hannes-hochreiner/sensor-net-gateway-bl651/box/src/bottom.3d.scad

use <bottom.2d.scad>;

linear_extrude(height = 2, center = true, convexity = 10, twist = 0) {
  bottom();
}
