hannes-hochreiner/sensor-net-gateway-bl651/box/src/box_mount.2d.scad

module box_mount() {
  difference() {
    polygon(points=[
          [-3,-3],
          [3,-3],
          [3,3],
          [-3,3],
        ],convexity=10);
    circle(d=3.2, $fn=50);
  }
}

box_mount();
