hannes-hochreiner/sensor-net-gateway-bl651/box/src/combined.scad

include <front.3d.scad>
include <top.3d.scad>
include <left.3d.scad>
