hannes-hochreiner/sensor-net-gateway-bl651/box/src/front.2d.scad

use <../lib/side.scad>

module front() {
  side_front_back(36,12,2);
}

front();
