hannes-hochreiner/sensor-net-gateway-bl651/box/src/left.2d.scad

use <../lib/side.scad>

module left() {
  side_left_right(50.2,12,2);
}

left();
