hannes-hochreiner/sensor-net-gateway-bl651/box/src/mounting.3d.scad

use <mounting.2d.scad>;

linear_extrude(height = 2, center = true, convexity = 10, twist = 0) {
  mounting();
}
