hannes-hochreiner/sensor-net-gateway-bl651/box/src/pcb_mount.2d.scad

module pcb_mount() {
  difference() {
    circle(d=5.9, $fn=50);
    circle(d=3.2, $fn=50);
  }
}

pcb_mount();
