hannes-hochreiner/sensor-net-gateway-bl651/box/src/pcb_mount.3d.scad

use <pcb_mount.2d.scad>;

linear_extrude(height = 2, center = true, convexity = 10, twist = 0) {
  pcb_mount();
}
